josbouten/Pedal-O-Matic/schematic/pedal-o-matic.sch

## KiCad design schematic/pedal-o-matic.sch (2020-07-03)

Schematic: pedal-o-matic.sch

Parts:
A1: Arduino_Nano_v3.x; Arduino_Nano
D1, D2, D3, D4, D9, D10, D11, D12: 1N4148; D_DO-35_SOD27_P7.62mm_Horizontal
D5, D6, D7, D8: Blue LED; LED_D3.0mm
J1: Midi Out
J2: Conn_01x08_MountingPin
J3: Euro Rack Power Connector; DIN41612_B2_2x8_Male_Horizontal_THT
J4, J5, J6, J7: AudioJack3; Jack_6.35mm_Neutrik_NJ2FD-V_Vertical
J8, J9, J10, J11: AudioJack2; Jack_3.5mm_PJ311_Horizontal
Q1: BC557; TO-92_Inline
Q2: BC547; TO-92_Inline
R1, R2, R3, R4, R5, R6, R8: 100K; R_Axial_DIN0207_L6.3mm_D2.5mm_P7.62mm_Horizontal
R7: 2K; R_Axial_DIN0207_L6.3mm_D2.5mm_P7.62mm_Horizontal
R9, R11, R12, R13, R14, R15, R16: 10K; R_Axial_DIN0207_L6.3mm_D2.5mm_P7.62mm_Horizontal
R10, R17: 220; R_Axial_DIN0207_L6.3mm_D2.5mm_P7.62mm_Horizontal
RV1: 200k; R_Axial_DIN0207_L6.3mm_D2.5mm_P7.62mm_Horizontal
U1: TL1021; DIP-8_W10.16mm

Notes on the sheet:
3.5 mm jack CV output
Pedal-O-Matic is designed to handle 4 foot pedals. For each pedal one TL074 (4 op-amps) is needed. The sub sheets show the op-amp schematics.
6.35 mm jack pedal input
