josbouten/Pedal-O-Matic/schematic/pedal_01_opamps.sch

## KiCad design schematic/pedal_01_opamps.sch (2020-06-30)

Schematic: pedal_01_opamps.sch

Parts:
D13, D15: 1N4148; D_DO-35_SOD27_P7.62mm_Horizontal
D14: Green LED; LED_D3.0mm
D16: Yellow LED; LED_D3.0mm-3
R18, R19, R20, R21, R23, R24, R28, R29, R30, R31, R32, R33: 100K; R_Axial_DIN0207_L6.3mm_D2.5mm_P7.62mm_Horizontal
R22: 1K; R_Axial_DIN0207_L6.3mm_D2.5mm_P7.62mm_Horizontal
R25: 3K3; R_Axial_DIN0207_L6.3mm_D2.5mm_P7.62mm_Horizontal
R26, R27: 4k7; R_Axial_DIN0207_L6.3mm_D2.5mm_P7.62mm_Horizontal
RV2, RV3: 100K; R_Axial_DIN0207_L6.3mm_D2.5mm_P7.62mm_Horizontal
SW1: -5V : 5V / 0V : 5V
U2: TL074; DIP_Socket-14_W4.3_W5.08_W7.62_W10.16_W10.9_3M_214-3339-00-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

Notes on the sheet:
SUBTRACT
Calibrate the Green and Yellow LEDs so that the yellow led starts to light when Vout goes just below 0 V and the green led starts to light when Vout goes just above 0 V. For the yellow LED you will need a Volt meter to do this. For the green LED the calibration is simplified if you set the switch t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
