josbouten/Pedal-O-Matic/schematic/pedal_02_opamps.sch

## KiCad design schematic/pedal_02_opamps.sch (2020-06-30)

Schematic: pedal_02_opamps.sch

Parts:
D17, D19: 1N4148; D_DO-35_SOD27_P7.62mm_Horizontal
D18: Green LED; LED_D3.0mm
D20: Yellow LED; LED_D3.0mm
R34, R35, R36, R37, R39, R40, R44, R45, R46, R47, R48, R49: 100K; R_Axial_DIN0207_L6.3mm_D2.5mm_P7.62mm_Horizontal
R38: 1K; R_Axial_DIN0207_L6.3mm_D2.5mm_P7.62mm_Horizontal
R41: 3K3; R_Axial_DIN0207_L6.3mm_D2.5mm_P7.62mm_Horizontal
R42, R43: 4k7; R_Axial_DIN0207_L6.3mm_D2.5mm_P7.62mm_Horizontal
RV4, RV5: 100K; R_Axial_DIN0207_L6.3mm_D2.5mm_P7.62mm_Horizontal
SW2: -5V : 5V / 0V : 5V
U3: TL074; DIP_Socket-14_W4.3_W5.08_W7.62_W10.16_W10.9_3M_214-3339-00-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

Notes on the sheet:
SUBTRACT
Calibrate the Green and Yellow LEDs so that the yellow led starts to light when Vout goes just below 0 V and the green led starts to light when Vout goes just above 0 V. For the yellow LED you will need a Volt meter to do this. For the green LED the calibration is simplified if you set the switch t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
