josbouten/Pedal-O-Matic/schematic/pedal_04_opamps.sch

## KiCad design schematic/pedal_04_opamps.sch (2020-06-30)

Schematic: pedal_04_opamps.sch

Parts:
D25, D27: 1N4148; D_DO-35_SOD27_P7.62mm_Horizontal
D26: Green LED; LED_D3.0mm
D28: Yellow LED; LED_D3.0mm
R66, R67, R68, R69, R71, R72, R76, R77, R78, R79, R80, R81: 100K; R_Axial_DIN0207_L6.3mm_D2.5mm_P7.62mm_Horizontal
R70: 1K; R_Axial_DIN0207_L6.3mm_D2.5mm_P7.62mm_Horizontal
R73: 3K3; R_Axial_DIN0207_L6.3mm_D2.5mm_P7.62mm_Horizontal
R74, R75: 4k7; R_Axial_DIN0207_L6.3mm_D2.5mm_P7.62mm_Horizontal
RV8, RV9: 100K; R_Axial_DIN0207_L6.3mm_D2.5mm_P7.62mm_Horizontal
SW4: -5V : 5V / 0V : 5V
U5: TL074; DIP_Socket-14_W4.3_W5.08_W7.62_W10.16_W10.9_3M_214-3339-00-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

Notes on the sheet:
SUBTRACT
Calibrate the Green and Yellow LEDs so that the yellow led starts to light when Vout goes just below 0 V and the green led starts to light when Vout goes just above 0 V. For the yellow LED you will need a Volt meter to do this. For the green LED the calibration is simplified if you set the switch t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
